pankev-in/GCER_OPEN_2014/Software/Tests/Grab/.build/mega2560/src/Test_GRAB.cpp

#include <Arduino.h>
#include <Servo.h>
void setup();
void loop();
void OpenGrab();
void CloseGrab();
#line 1 "src/Test_GRAB.ino"
//#include <Servo.h>

Servo SERVO_GRAB;
#define NUM_SERVO_GRAB_CLOSE 0
#define NUM_SERVO_GRAB_OPEN 100
#define SERVO_GRAB_PIN  6
void setup(){
  SERVO_GRAB.attach(SERVO_GRAB_PIN);
}

void loop(){
  OpenGrab();
  delay(1000);
  CloseGrab();
  delay(5000);
}

void OpenGrab(){
  SERVO_GRAB.write(NUM_SERVO_GRAB_OPEN);
}

// Open the grabbler:
// Status: Untested
void CloseGrab(){
  SERVO_GRAB.write(NUM_SERVO_GRAB_CLOSE);
}
